talos-robotics/Pocket-breille-project/photos/viomatiko/81.jpg

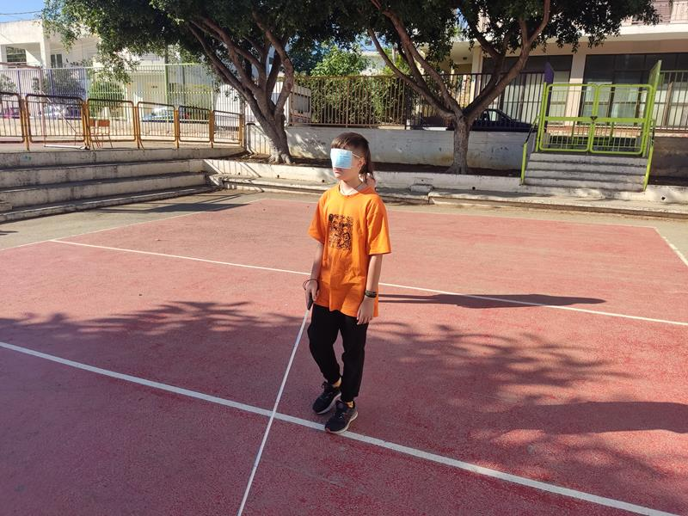
photos/viomatiko/81.jpg
