talos-robotics/Pocket-breille-project/photos/viomatiko/83.jpg

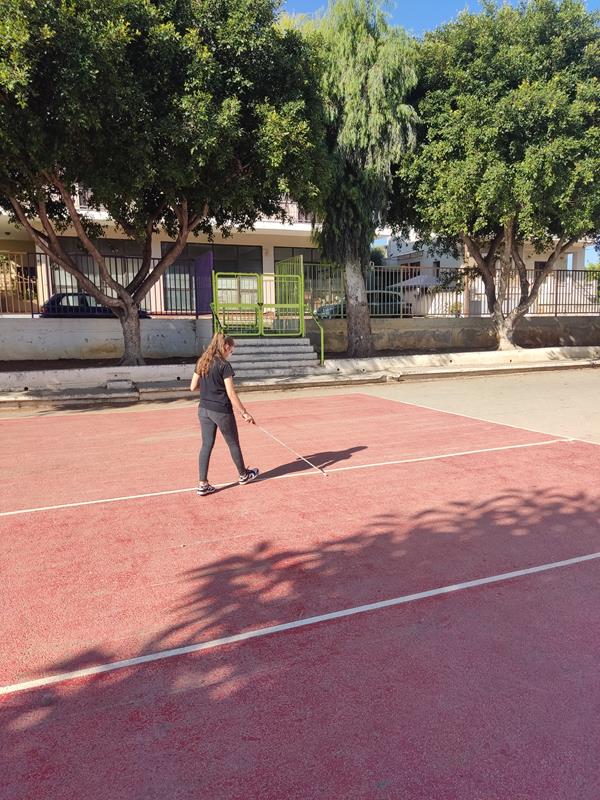
photos/viomatiko/83.jpg
