talos-robotics/Pocket-breille-project/photos/viomatiko/84.jpg

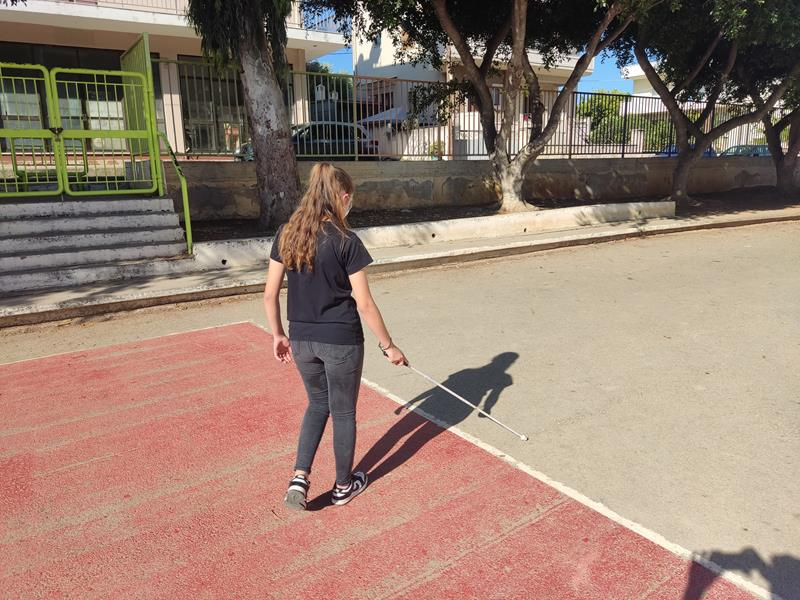
photos/viomatiko/84.jpg
